russery/fm-streamer/docs/fm_output.png

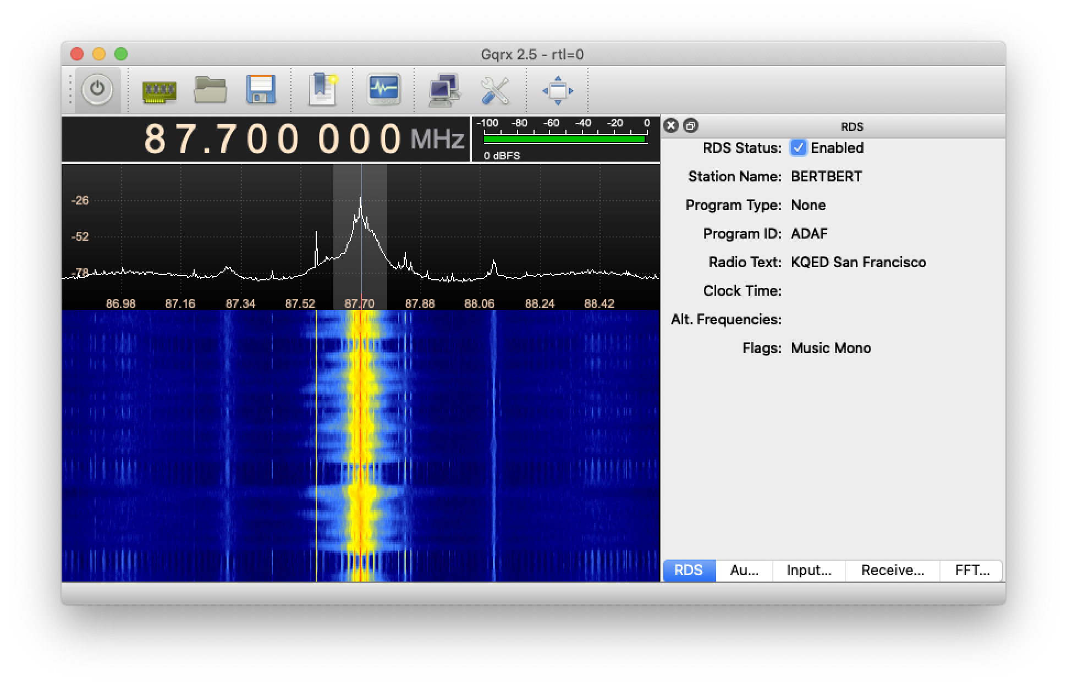
docs/fm_output.png
