russery/fm-streamer/hardware/resources/kicad-master/documentation/aht10_breakout/images/3d_silk.png

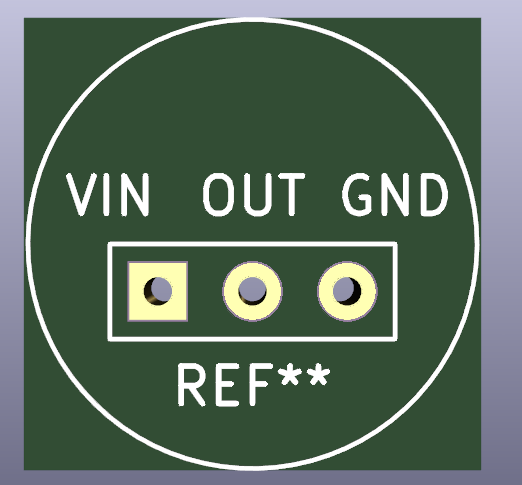
hardware/resources/kicad-master/documentation/aht10_breakout/images/3d_silk.png
