russery/fm-streamer/hardware/resources/kicad-master/documentation/aht10_breakout/images/footprint.png

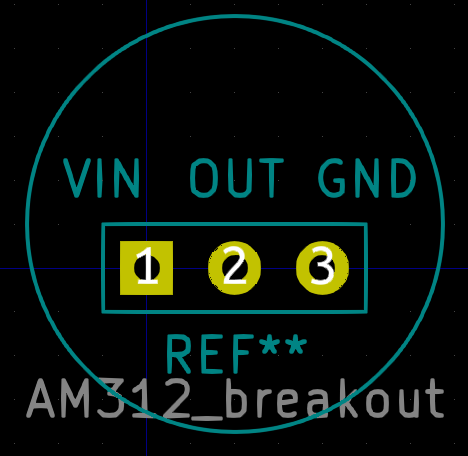
hardware/resources/kicad-master/documentation/aht10_breakout/images/footprint.png
