russery/fm-streamer/hardware/resources/kicad-master/documentation/aht10_breakout/images/picture.jpg

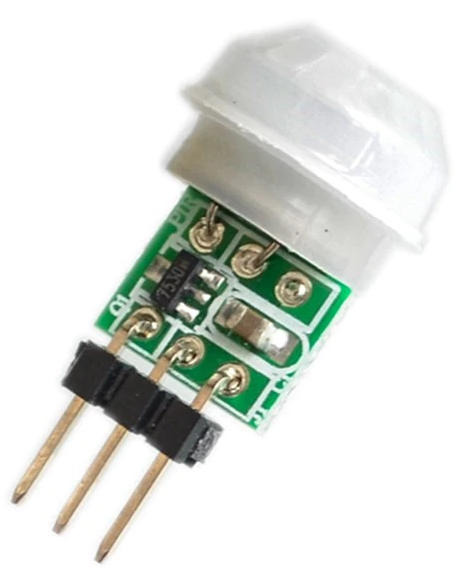
hardware/resources/kicad-master/documentation/aht10_breakout/images/picture.jpg
