russery/fm-streamer/hardware/resources/kicad-master/documentation/aht10_breakout/images/symbol.png

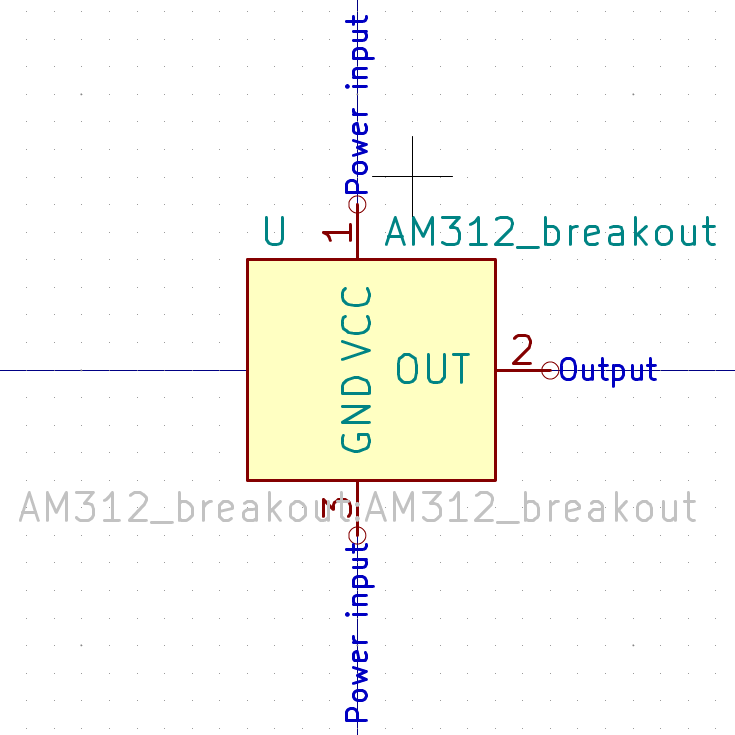
hardware/resources/kicad-master/documentation/aht10_breakout/images/symbol.png
