russery/fm-streamer/hardware/resources/kicad-master/documentation/esp32_devkit_v1_doit/images/3d_silk.png

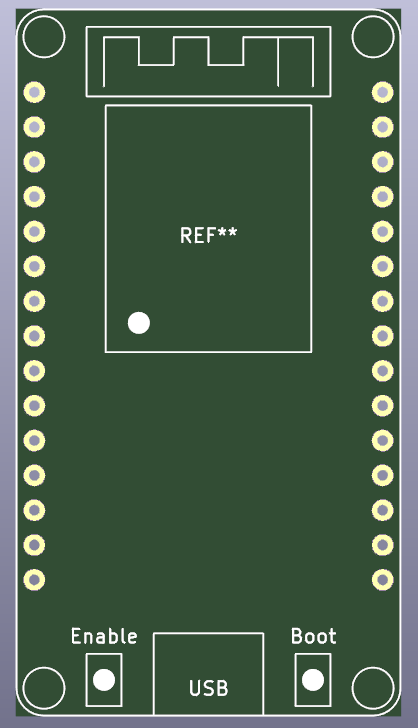
hardware/resources/kicad-master/documentation/esp32_devkit_v1_doit/images/3d_silk.png
