russery/fm-streamer/hardware/resources/kicad-master/documentation/esp32_devkit_v1_doit/images/picture.jpg

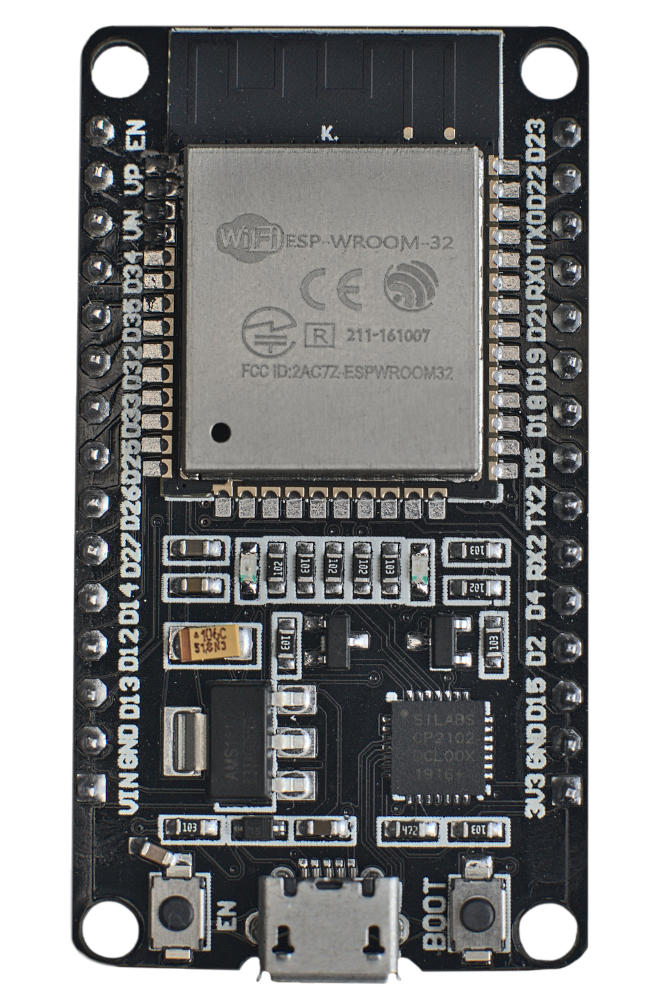
hardware/resources/kicad-master/documentation/esp32_devkit_v1_doit/images/picture.jpg
