russery/fm-streamer/hardware/resources/kicad-master/documentation/esp32_devkit_v1_doit/images/symbol.png

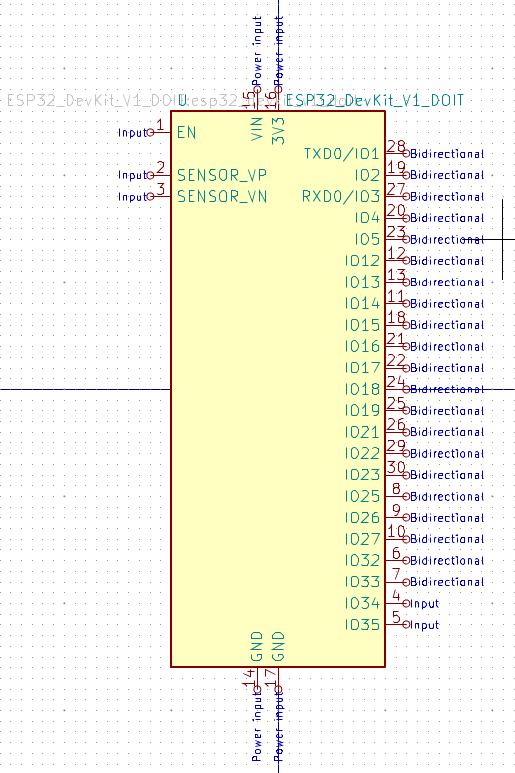
hardware/resources/kicad-master/documentation/esp32_devkit_v1_doit/images/symbol.png
