russery/fm-streamer/hardware/resources/kicad-master/documentation/kf301_5.0/images/3d_silk.png

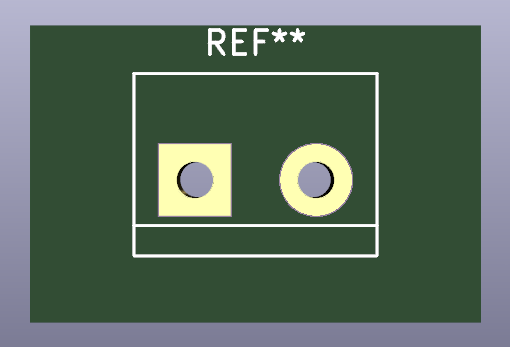
hardware/resources/kicad-master/documentation/kf301_5.0/images/3d_silk.png
