russery/fm-streamer/hardware/resources/kicad-master/documentation/kf301_5.0/images/3d_top.png

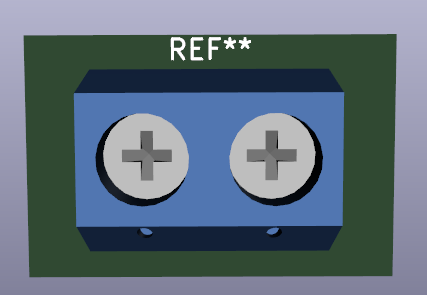
hardware/resources/kicad-master/documentation/kf301_5.0/images/3d_top.png
