russery/fm-streamer/hardware/resources/kicad-master/documentation/kf301_5.0/images/footprint.png

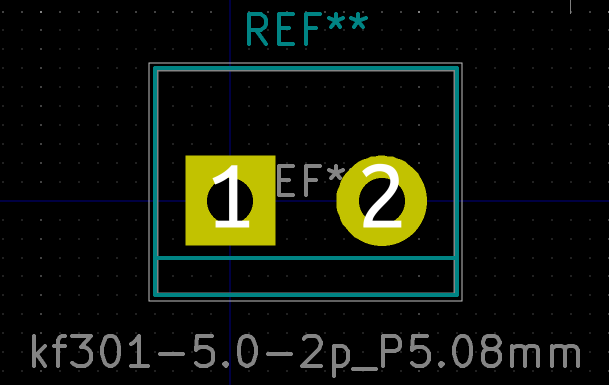
hardware/resources/kicad-master/documentation/kf301_5.0/images/footprint.png
