russery/fm-streamer/hardware/resources/kicad-master/documentation/kf301_5.0/images/picture.jpg

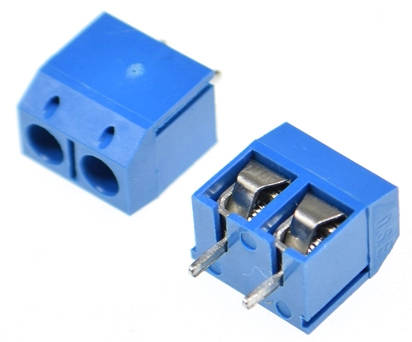
hardware/resources/kicad-master/documentation/kf301_5.0/images/picture.jpg
